Pedrolino-X/RPi-Monitor-Car/上位机软件代码/Camera_Photos/capture_2025-07-13_23-57-23.jpg

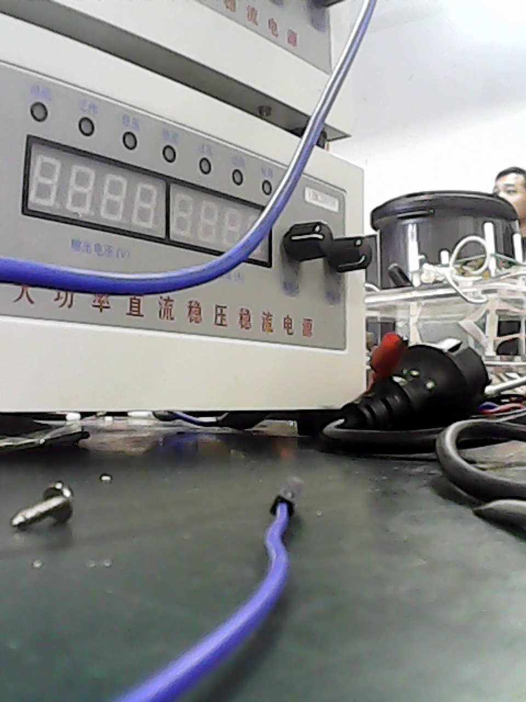
上位机软件代码/Camera_Photos/capture_2025-07-13_23-57-23.jpg
